briandye6/Mesh-Networking/src/lcd.c

//============================================================================
// lcd.c: Adapted from the lcdwiki.com examples.
//============================================================================

#include "stm32f0xx.h"
#include <stdint.h>
#include "lcd.h"

lcd_dev_t lcddev;

// What GPIO port and SPI channel are we using here?
#define GPIO_TYPE  GPIOA
#define SPI SPI1

#define LCD_CS    4 /* also known as NSS */
#define LCD_RS    3
#define LCD_RESET 2

#define LCD_CS_SET  do { while((SPI->SR & SPI_SR_BSY) != 0); GPIO_TYPE->BSRR=1<<LCD_CS; } while(0)
#define LCD_RS_SET  GPIO_TYPE->BSRR=1<<LCD_RS
#define LCD_RESET_SET GPIO_TYPE->BSRR=1<<LCD_RESET

#define LCD_CS_CLR  GPIO_TYPE->BRR=1<<LCD_CS
#define LCD_RS_CLR  GPIO_TYPE->BRR=1<<LCD_RS
#define LCD_RESET_CLR GPIO_TYPE->BRR=1<<LCD_RESET

//============================================================================
// Wait for n nanoseconds. (Maximum: 4.294 seconds)
//============================================================================
void nano_wait(unsigned int n) {
    asm(    "        mov r0,%0\n"
            "repeat: sub r0,#83\n"
            "        bgt repeat\n" : : "r"(n) : "r0", "cc");
}



void LCD_EXTI6_Initialize(void) {
  // Configure PC6 as Input
  RCC->AHBENR |= RCC_AHBENR_GPIOCEN;
  GPIOC->MODER &= ~(3<<12);
  GPIOC->PUPDR |= (GPIO_PuPd_DOWN << 12);

  // Configure SYSCFG
  RCC->APB2ENR |= RCC_APB2ENR_SYSCFGEN;

  // Select PC6 as the trigger source of EXTI1
  SYSCFG->EXTICR[1] &= ~SYSCFG_EXTICR2_EXTI6;
  SYSCFG->EXTICR[1] |= SYSCFG_EXTICR2_EXTI6_PC;


  // Enable Rising Edge Trigger for EXTI6
  EXTI->RTSR |= EXTI_RTSR_TR6;

  // Disable Falling edge trigger for EXTI6
  EXTI->FTSR &= ~EXTI_FTSR_TR6;

  // Enable EXTI1 interrupt
  EXTI->IMR |= EXTI_IMR_MR6;

  // Set EXTI6 Priority to be 0
  NVIC_SetPriority(7, 0);

  // Enable EXTI6 Interrupt
  NVIC_EnableIRQ(7);


}



void LCD_Reset(void)
{
    // Assert reset
    GPIOA->BRR = 1<<LCD_RESET;
    nano_wait(100000000);
    GPIOA->BSRR = 1<<LCD_RESET;
    nano_wait(50000000);
}

// If you want to try the slower version of SPI, #define SLOW_SPI
//#define SLOW_SPI
#if defined(SLOW_SPI)

// Write a byte to SPI.
void SPI_WriteByte(uint8_t Data)
{
    while((SPI->SR & SPI_SR_TXE) == 0)
        ;
    *((uint8_t*)&SPI->DR) = Data;
}

// Write to an LCD "register"
void LCD_WR_REG(uint8_t data)
{
    LCD_RS_CLR;
    LCD_CS_CLR;
    SPI_WriteByte(data);
    LCD_CS_SET;
}

// Write 8-bit data to the LCD
void LCD_WR_DATA(uint8_t data)
{
    LCD_RS_SET;
    LCD_CS_CLR;
    SPI_WriteByte(data);
    LCD_CS_SET;
}

// Prepare to write 16-bit data to the LCD
void LCD_WriteData16_Prepare()
{
    LCD_RS_SET;
}

// Write 16-bit data
void LCD_WriteData16(u16 Data)
{
    LCD_CS_CLR;
    SPI_WriteByte(Data>>8);
    SPI_WriteByte(Data);
    LCD_CS_SET;
}

// Finish writing 16-bit data
void LCD_WriteData16_End()
{
}

#else /* not SLOW_SPI */

// Write to an LCD "register"
void LCD_WR_REG(uint8_t data)
{
    while((SPI->SR & SPI_SR_BSY) != 0)
        ;
    // Don't clear RS until the previous operation is done.
    LCD_RS_CLR;
    *((uint8_t*)&SPI->DR) = data;
}

// Write 8-bit data to the LCD
void LCD_WR_DATA(uint8_t data)
{
    while((SPI->SR & SPI_SR_BSY) != 0)
        ;
    // Don't set RS until the previous operation is done.
    LCD_RS_SET;
    *((uint8_t*)&SPI->DR) = data;
}

// Prepare to write 16-bit data to the LCD
void LCD_WriteData16_Prepare()
{
    LCD_RS_SET;
    SPI->CR2 |= SPI_CR2_DS;
}

// Write 16-bit data
void LCD_WriteData16(u16 data)
{
    while((SPI->SR & SPI_SR_TXE) == 0)
        ;
    SPI->DR = data;
}

// Finish writing 16-bit data
void LCD_WriteData16_End()
{
    SPI->CR2 &= ~SPI_CR2_DS; // bad value forces it back to 8-bit mode
}
#endif /* not SLOW_SPI */

// Select an LCD "register" and write 8-bit data to it.
void LCD_WriteReg(uint8_t LCD_Reg, uint16_t LCD_RegValue)
{
    LCD_WR_REG(LCD_Reg);
    LCD_WR_DATA(LCD_RegValue);
}

// Issue the "write RAM" command configured for the display.
void LCD_WriteRAM_Prepare(void)
{
    LCD_WR_REG(lcddev.wramcmd);
}

// Configure the lcddev fields for the display orientation.
void LCD_direction(u8 direction)
{
    lcddev.setxcmd=0x2A;
    lcddev.setycmd=0x2B;
    lcddev.wramcmd=0x2C;
    switch(direction){
    case 0:
        lcddev.width=LCD_W;
        lcddev.height=LCD_H;
        LCD_WriteReg(0x36,(1<<3)|(0<<6)|(0<<7));//BGR==1,MY==0,MX==0,MV==0
        break;
    case 1:
        lcddev.width=LCD_H;
        lcddev.height=LCD_W;
        LCD_WriteReg(0x36,(1<<3)|(0<<7)|(1<<6)|(1<<5));//BGR==1,MY==1,MX==0,MV==1
        break;
    case 2:
        lcddev.width=LCD_W;
        lcddev.height=LCD_H;
        LCD_WriteReg(0x36,(1<<3)|(1<<6)|(1<<7));//BGR==1,MY==0,MX==0,MV==0
        break;
    case 3:
        lcddev.width=LCD_H;
        lcddev.height=LCD_W;
        LCD_WriteReg(0x36,(1<<3)|(1<<7)|(1<<5));//BGR==1,MY==1,MX==0,MV==1
        break;
    default:break;
    }
}

// Do the initialization sequence for the display.
void LCD_Init()
{
    LCD_Reset();
    // Initialization sequence for 2.2inch ILI9341
    LCD_WR_REG(0xCF);
    LCD_WR_DATA(0x00);
    LCD_WR_DATA(0xD9); // C1
    LCD_WR_DATA(0X30);
    LCD_WR_REG(0xED);
    LCD_WR_DATA(0x64);
    LCD_WR_DATA(0x03);
    LCD_WR_DATA(0X12);
    LCD_WR_DATA(0X81);
    LCD_WR_REG(0xE8);
    LCD_WR_DATA(0x85);
    LCD_WR_DATA(0x10);
    LCD_WR_DATA(0x7A);
    LCD_WR_REG(0xCB);
    LCD_WR_DATA(0x39);
    LCD_WR_DATA(0x2C);
    LCD_WR_DATA(0x00);
    LCD_WR_DATA(0x34);
    LCD_WR_DATA(0x02);
    LCD_WR_REG(0xF7);
    LCD_WR_DATA(0x20);
    LCD_WR_REG(0xEA);
    LCD_WR_DATA(0x00);
    LCD_WR_DATA(0x00);
    LCD_WR_REG(0xC0);    // Power control
    LCD_WR_DATA(0x21);   // VRH[5:0]  //1B
    LCD_WR_REG(0xC1);    // Power control
    LCD_WR_DATA(0x12);   // SAP[2:0];BT[3:0] //01
    LCD_WR_REG(0xC5);    // VCM control
    LCD_WR_DATA(0x39);   // 3F
    LCD_WR_DATA(0x37);   // 3C
    LCD_WR_REG(0xC7);    // VCM control2
    LCD_WR_DATA(0XAB);   // B0
    LCD_WR_REG(0x36);    // Memory Access Control
    LCD_WR_DATA(0x48);
    LCD_WR_REG(0x3A);
    LCD_WR_DATA(0x55);
    LCD_WR_REG(0xB1);
    LCD_WR_DATA(0x00);
    LCD_WR_DATA(0x1B);   // 1A
    LCD_WR_REG(0xB6);    // Display Function Control
    LCD_WR_DATA(0x0A);
    LCD_WR_DATA(0xA2);
    LCD_WR_REG(0xF2);    // 3Gamma Function Disable
    LCD_WR_DATA(0x00);
    LCD_WR_REG(0x26);    // Gamma curve selected
    LCD_WR_DATA(0x01);

    LCD_WR_REG(0xE0);     // Set Gamma
    LCD_WR_DATA(0x0F);
    LCD_WR_DATA(0x23);
    LCD_WR_DATA(0x1F);
    LCD_WR_DATA(0x0B);
    LCD_WR_DATA(0x0E);
    LCD_WR_DATA(0x08);
    LCD_WR_DATA(0x4B);
    LCD_WR_DATA(0XA8);
    LCD_WR_DATA(0x3B);
    LCD_WR_DATA(0x0A);
    LCD_WR_DATA(0x14);
    LCD_WR_DATA(0x06);
    LCD_WR_DATA(0x10);
    LCD_WR_DATA(0x09);
    LCD_WR_DATA(0x00);
    LCD_WR_REG(0XE1);      // Set Gamma
    LCD_WR_DATA(0x00);
    LCD_WR_DATA(0x1C);
    LCD_WR_DATA(0x20);
    LCD_WR_DATA(0x04);
    LCD_WR_DATA(0x10);
    LCD_WR_DATA(0x08);
    LCD_WR_DATA(0x34);
    LCD_WR_DATA(0x47);
    LCD_WR_DATA(0x44);
    LCD_WR_DATA(0x05);
    LCD_WR_DATA(0x0B);
    LCD_WR_DATA(0x09);
    LCD_WR_DATA(0x2F);
    LCD_WR_DATA(0x36);
    LCD_WR_DATA(0x0F);
    LCD_WR_REG(0x2B);
    LCD_WR_DATA(0x00);
    LCD_WR_DATA(0x00);
    LCD_WR_DATA(0x01);
    LCD_WR_DATA(0x3f);
    LCD_WR_REG(0x2A);
    LCD_WR_DATA(0x00);
    LCD_WR_DATA(0x00);
    LCD_WR_DATA(0x00);
    LCD_WR_DATA(0xef);
    LCD_WR_REG(0x11);     // Exit Sleep
    nano_wait(120000000); // Wait 120 ms
    LCD_WR_REG(0x29);     // Display on

    LCD_direction(USE_HORIZONTAL);
}

//===========================================================================
// Set the entire display to one color
//===========================================================================
void LCD_Clear(u16 Color)
{
    unsigned int i,m;
    LCD_SetWindow(0,0,lcddev.width-1,lcddev.height-1);
    LCD_WriteData16_Prepare();
    for(i=0;i<lcddev.height;i++)
    {
        for(m=0;m<lcddev.width;m++)
        {
            LCD_WriteData16(Color);
        }
    }
    LCD_WriteData16_End();
}

//===========================================================================
// Select a subset of the display to work on, and issue the "Write RAM"
// command to prepare to send pixel data to it.
//===========================================================================
void LCD_SetWindow(uint16_t xStart, uint16_t yStart, uint16_t xEnd, uint16_t yEnd)
{
    LCD_WR_REG(lcddev.setxcmd);
    LCD_WR_DATA(xStart>>8);
    LCD_WR_DATA(0x00FF&xStart);
    LCD_WR_DATA(xEnd>>8);
    LCD_WR_DATA(0x00FF&xEnd);

    LCD_WR_REG(lcddev.setycmd);
    LCD_WR_DATA(yStart>>8);
    LCD_WR_DATA(0x00FF&yStart);
    LCD_WR_DATA(yEnd>>8);
    LCD_WR_DATA(0x00FF&yEnd);

    LCD_WriteRAM_Prepare();
}

//===========================================================================
// Draw a single dot of color c at (x,y)
//===========================================================================
void LCD_DrawPoint(u16 x, u16 y, u16 c)
{
    LCD_SetWindow(x,y,x,y);
    LCD_WriteData16_Prepare();
    LCD_WriteData16(c);
    LCD_WriteData16_End();
}

//===========================================================================
// Draw a line of color c from (x1,y1) to (x2,y2).
//===========================================================================
void LCD_DrawLine(u16 x1, u16 y1, u16 x2, u16 y2, u16 c)
{
    u16 t;
    int xerr=0,yerr=0,delta_x,delta_y,distance;
    int incx,incy,uRow,uCol;

    delta_x=x2-x1;
    delta_y=y2-y1;
    uRow=x1;
    uCol=y1;
    if(delta_x>0)incx=1;
    else if(delta_x==0)incx=0;
    else {incx=-1;delta_x=-delta_x;}
    if(delta_y>0)incy=1;
    else if(delta_y==0)incy=0;
    else{incy=-1;delta_y=-delta_y;}
    if( delta_x>delta_y)distance=delta_x;
    else distance=delta_y;
    for(t=0;t<=distance+1;t++ )
    {
        LCD_DrawPoint(uRow,uCol,c);
        xerr+=delta_x ;
        yerr+=delta_y ;
        if(xerr>distance)
        {
            xerr-=distance;
            uRow+=incx;
        }
        if(yerr>distance)
        {
            yerr-=distance;
            uCol+=incy;
        }
    }
}

//===========================================================================
// Draw a rectangle of lines of color c from (x1,y1) to (x2,y2).
//===========================================================================
void LCD_DrawRectangle(u16 x1, u16 y1, u16 x2, u16 y2, u16 c)
{
    LCD_DrawLine(x1,y1,x2,y1,c);
    LCD_DrawLine(x1,y1,x1,y2,c);
    LCD_DrawLine(x1,y2,x2,y2,c);
    LCD_DrawLine(x2,y1,x2,y2,c);
}

//===========================================================================
// Fill a rectangle with color c from (x1,y1) to (x2,y2).
//===========================================================================
void LCD_Fill(u16 sx,u16 sy,u16 ex,u16 ey,u16 color)
{
    u16 i,j;
    u16 width=ex-sx+1;
    u16 height=ey-sy+1;
    LCD_SetWindow(sx,sy,ex,ey);
    LCD_WriteData16_Prepare();
    for(i=0;i<height;i++)
    {
        for(j=0;j<width;j++)
        LCD_WriteData16(color);
    }
    LCD_WriteData16_End();
}

//===========================================================================
// Draw a filled rectangle of lines of color c from (x1,y1) to (x2,y2).
//===========================================================================
void LCD_DrawFillRectangle(u16 x1, u16 y1, u16 x2, u16 y2, u16 c)
{
    LCD_Fill(x1,y1,x2,y2,c);
}

static void _draw_circle_8(int xc, int yc, int x, int y, u16 c)
{
    LCD_DrawPoint(xc + x, yc + y, c);
    LCD_DrawPoint(xc - x, yc + y, c);
    LCD_DrawPoint(xc + x, yc - y, c);
    LCD_DrawPoint(xc - x, yc - y, c);
    LCD_DrawPoint(xc + y, yc + x, c);
    LCD_DrawPoint(xc - y, yc + x, c);
    LCD_DrawPoint(xc + y, yc - x, c);
    LCD_DrawPoint(xc - y, yc - x, c);
}

//===========================================================================
// Draw a circle of color c and radius r at center (xc,yc).
// The fill parameter indicates if it is to be filled.
//===========================================================================
void LCD_Circle(u16 xc, u16 yc, u16 r, u16 fill, u16 c)
{
    int x = 0, y = r, yi, d;
    d = 3 - 2 * r;

    if (fill)
    {
        while (x <= y) {
            for (yi = x; yi <= y; yi++)
                _draw_circle_8(xc, yc, x, yi, c);

            if (d < 0) {
                d = d + 4 * x + 6;
            } else {
                d = d + 4 * (x - y) + 10;
                y--;
            }
            x++;
        }
    } else
    {
        while (x <= y) {
            _draw_circle_8(xc, yc, x, y, c);
            if (d < 0) {
                d = d + 4 * x + 6;
            } else {
                d = d + 4 * (x - y) + 10;
                y--;
            }
            x++;
        }
    }
}

//===========================================================================
// Draw a triangle of lines of color c with vertices at (x0,y0), (x1,y1), (x2,y2).
//===========================================================================
void LCD_DrawTriangle(u16 x0,u16 y0,  u16 x1,u16 y1,  u16 x2,u16 y2, u16 c)
{
    LCD_DrawLine(x0,y0,x1,y1,c);
    LCD_DrawLine(x1,y1,x2,y2,c);
    LCD_DrawLine(x2,y2,x0,y0,c);
}

static void _swap(u16 *a, u16 *b)
{
    u16 tmp;
    tmp = *a;
    *a = *b;
    *b = tmp;
}

//===========================================================================
// Draw a filled triangle of color c with vertices at (x0,y0), (x1,y1), (x2,y2).
//===========================================================================
void LCD_DrawFillTriangle(u16 x0,u16 y0, u16 x1,u16 y1, u16 x2,u16 y2, u16 c)
{
    u16 a, b, y, last;
    int dx01, dy01, dx02, dy02, dx12, dy12;
    long sa = 0;
    long sb = 0;
    if (y0 > y1)
    {
    _swap(&y0,&y1);
        _swap(&x0,&x1);
    }
    if (y1 > y2)
    {
    _swap(&y2,&y1);
        _swap(&x2,&x1);
    }
  if (y0 > y1)
    {
    _swap(&y0,&y1);
        _swap(&x0,&x1);
  }
    if(y0 == y2)
    {
        a = b = x0;
        if(x1 < a)
    {
            a = x1;
    }
    else if(x1 > b)
    {
            b = x1;
    }
    if(x2 < a)
    {
            a = x2;
    }
        else if(x2 > b)
    {
            b = x2;
    }
        LCD_Fill(a,y0,b,y0,c);
    return;
    }
    dx01 = x1 - x0;
    dy01 = y1 - y0;
    dx02 = x2 - x0;
    dy02 = y2 - y0;
    dx12 = x2 - x1;
    dy12 = y2 - y1;

    if(y1 == y2)
    {
        last = y1;
    }
  else
    {
        last = y1-1;
    }
    for(y=y0; y<=last; y++)
    {
        a = x0 + sa / dy01;
        b = x0 + sb / dy02;
        sa += dx01;
    sb += dx02;
    if(a > b)
    {
            _swap(&a,&b);
        }
        LCD_Fill(a,y,b,y,c);
    }
    sa = dx12 * (y - y1);
    sb = dx02 * (y - y0);
    for(; y<=y2; y++)
    {
        a = x1 + sa / dy12;
        b = x0 + sb / dy02;
        sa += dx12;
        sb += dx02;
        if(a > b)
        {
            _swap(&a,&b);
        }
        LCD_Fill(a,y,b,y,c);
    }
}

// A 12x6 font
const unsigned char asc2_1206[95][12]={
{0x00,0x00,0x00,0x00,0x00,0x00,0x00,0x00,0x00,0x00,0x00,0x00},/*" ",0*/
{0x00,0x00,0x04,0x04,0x04,0x04,0x04,0x04,0x00,0x04,0x00,0x00},/*"!",1*/
{0x00,0x14,0x0A,0x0A,0x00,0x00,0x00,0x00,0x00,0x00,0x00,0x00},/*""",2*/
{0x00,0x00,0x14,0x14,0x3F,0x14,0x0A,0x3F,0x0A,0x0A,0x00,0x00},/*"#",3*/
{0x00,0x04,0x1E,0x15,0x05,0x06,0x0C,0x14,0x15,0x0F,0x04,0x00},/*"$",4*/
{0x00,0x00,0x12,0x15,0x0D,0x0A,0x14,0x2C,0x2A,0x12,0x00,0x00},/*"%",5*/
{0x00,0x00,0x04,0x0A,0x0A,0x1E,0x15,0x15,0x09,0x36,0x00,0x00},/*"&",6*/
{0x00,0x02,0x02,0x01,0x00,0x00,0x00,0x00,0x00,0x00,0x00,0x00},/*"'",7*/
{0x00,0x20,0x10,0x08,0x08,0x08,0x08,0x08,0x08,0x10,0x20,0x00},/*"(",8*/
{0x00,0x02,0x04,0x08,0x08,0x08,0x08,0x08,0x08,0x04,0x02,0x00},/*")",9*/
{0x00,0x00,0x00,0x04,0x15,0x0E,0x0E,0x15,0x04,0x00,0x00,0x00},/*"*",10*/
{0x00,0x00,0x04,0x04,0x04,0x1F,0x04,0x04,0x04,0x00,0x00,0x00},/*"+",11*/
{0x00,0x00,0x00,0x00,0x00,0x00,0x00,0x00,0x00,0x02,0x02,0x01},/*",",12*/
{0x00,0x00,0x00,0x00,0x00,0x1F,0x00,0x00,0x00,0x00,0x00,0x00},/*"-",13*/
{0x00,0x00,0x00,0x00,0x00,0x00,0x00,0x00,0x00,0x02,0x00,0x00},/*".",14*/
{0x00,0x10,0x08,0x08,0x08,0x04,0x04,0x02,0x02,0x02,0x01,0x00},/*"/",15*/
{0x00,0x00,0x0E,0x11,0x11,0x11,0x11,0x11,0x11,0x0E,0x00,0x00},/*"0",16*/
{0x00,0x00,0x04,0x06,0x04,0x04,0x04,0x04,0x04,0x0E,0x00,0x00},/*"1",17*/
{0x00,0x00,0x0E,0x11,0x11,0x08,0x04,0x02,0x01,0x1F,0x00,0x00},/*"2",18*/
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
{0x00,0x00,0x00,0x40,0x20,0x10,0x08,0x04,0x02,0x04,0x08,0x10,0x20,0x40,0x00,0x00},/*"<",28*/
{0x00,0x00,0x00,0x00,0x00,0x00,0x7F,0x00,0x00,0x00,0x7F,0x00,0x00,0x00,0x00,0x00},/*"=",29*/
{0x00,0x00,0x00,0x02,0x04,0x08,0x10,0x20,0x40,0x20,0x10,0x08,0x04,0x02,0x00,0x00},/*">",30*/
{0x00,0x00,0x00,0x3C,0x42,0x42,0x46,0x40,0x20,0x10,0x10,0x00,0x18,0x18,0x00,0x00},/*"?",31*/
{0x00,0x00,0x00,0x1C,0x22,0x5A,0x55,0x55,0x55,0x55,0x2D,0x42,0x22,0x1C,0x00,0x00},/*"@",32*/
{0x00,0x00,0x00,0x08,0x08,0x18,0x14,0x14,0x24,0x3C,0x22,0x42,0x42,0xE7,0x00,0x00},/*"A",33*/
{0x00,0x00,0x00,0x1F,0x22,0x22,0x22,0x1E,0x22,0x42,0x42,0x42,0x22,0x1F,0x00,0x00},/*"B",34*/
{0x00,0x00,0x00,0x7C,0x42,0x42,0x01,0x01,0x01,0x01,0x01,0x42,0x22,0x1C,0x00,0x00},/*"C",35*/
{0x00,0x00,0x00,0x1F,0x22,0x42,0x42,0x42,0x42,0x42,0x42,0x42,0x22,0x1F,0x00,0x00},/*"D",36*/
{0x00,0x00,0x00,0x3F,0x42,0x12,0x12,0x1E,0x12,0x12,0x02,0x42,0x42,0x3F,0x00,0x00},/*"E",37*/
{0x00,0x00,0x00,0x3F,0x42,0x12,0x12,0x1E,0x12,0x12,0x02,0x02,0x02,0x07,0x00,0x00},/*"F",38*/
{0x00,0x00,0x00,0x3C,0x22,0x22,0x01,0x01,0x01,0x71,0x21,0x22,0x22,0x1C,0x00,0x00},/*"G",39*/
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
};

//===========================================================================
// Display a single character at position x,y on the screen.
// fc,bc are the foreground,background colors
// num is the ASCII character number
// size is the height of the character (either 12 or 16)
// When mode is set, the background will be transparent.
//===========================================================================
void LCD_DrawChar(u16 x,u16 y,u16 fc, u16 bc, char num, u8 size, u8 mode)
{
    u8 temp;
    u8 pos,t;
    num=num-' ';
    LCD_SetWindow(x,y,x+size/2-1,y+size-1);
    if (!mode) {
        LCD_WriteData16_Prepare();
        for(pos=0;pos<size;pos++) {
            if (size==12)
                temp=asc2_1206[num][pos];
            else
                temp=asc2_1608[num][pos];
            for (t=0;t<size/2;t++) {
                if (temp&0x01)
                    LCD_WriteData16(fc);
                else
                    LCD_WriteData16(bc);
                temp>>=1;

            }
        }
        LCD_WriteData16_End();
    } else {
        for(pos=0;pos<size;pos++)
        {
            if (size==12)
                temp=asc2_1206[num][pos];
            else
                temp=asc2_1608[num][pos];
            for (t=0;t<size/2;t++)
            {
                if(temp&0x01)
                    LCD_DrawPoint(x+t,y+pos,fc);
                temp>>=1;
            }
        }
    }
}

//===========================================================================
// Display a string of characters starting at location x,y.
// fc,bc are the foreground,background colors.
// p is the pointer to the string.
// size is the height of the character (either 12 or 16)
// When mode is set, the background will be transparent.
//===========================================================================
void LCD_DrawString(u16 x,u16 y, u16 fc, u16 bg, const char *p, u8 size, u8 mode)
{
    while((*p<='~')&&(*p>=' '))
    {
        if(x>(lcddev.width-1)||y>(lcddev.height-1))
        return;
        LCD_DrawChar(x,y,fc,bg,*p,size,mode);
        x+=size/2;
        p++;
    }
}

//===========================================================================
// Draw a picture with upper left corner at (x0,y0).
//===========================================================================
void LCD_DrawPicture(u16 x0, u16 y0, const Picture *pic)
{
    u16 x1 = x0 + pic->width-1;
    u16 y1 = y0 + pic->height-1;
    // No error handling.  Just loop forever if out-of-bounds.
    while (x0 >= lcddev.width)
        ;
    while (x1 >= lcddev.width)
        ;
    while (y0 >= lcddev.height)
        ;
    while (y1 >= lcddev.height)
        ;
    LCD_SetWindow(x0,y0,x1,y1);
    LCD_WriteData16_Prepare();

    u16 *data = (u16 *)pic->pixel_data;
    for(int y=0; y<pic->height; y++) {
        u16 *row = &data[y * pic->width];
        for(int x=0; x<pic->width; x++)
            LCD_WriteData16(*row++);
    }

    LCD_WriteData16_End();
}
